Majoras-Other-Mask/Arduino-Piano-Example-Sketches/Original CG Files/CG_PCB/CG_PCB_Import/CG_PCB_Import.kicad_pcb

## KiCad design narcise/narcise-redux.kicad_pcb

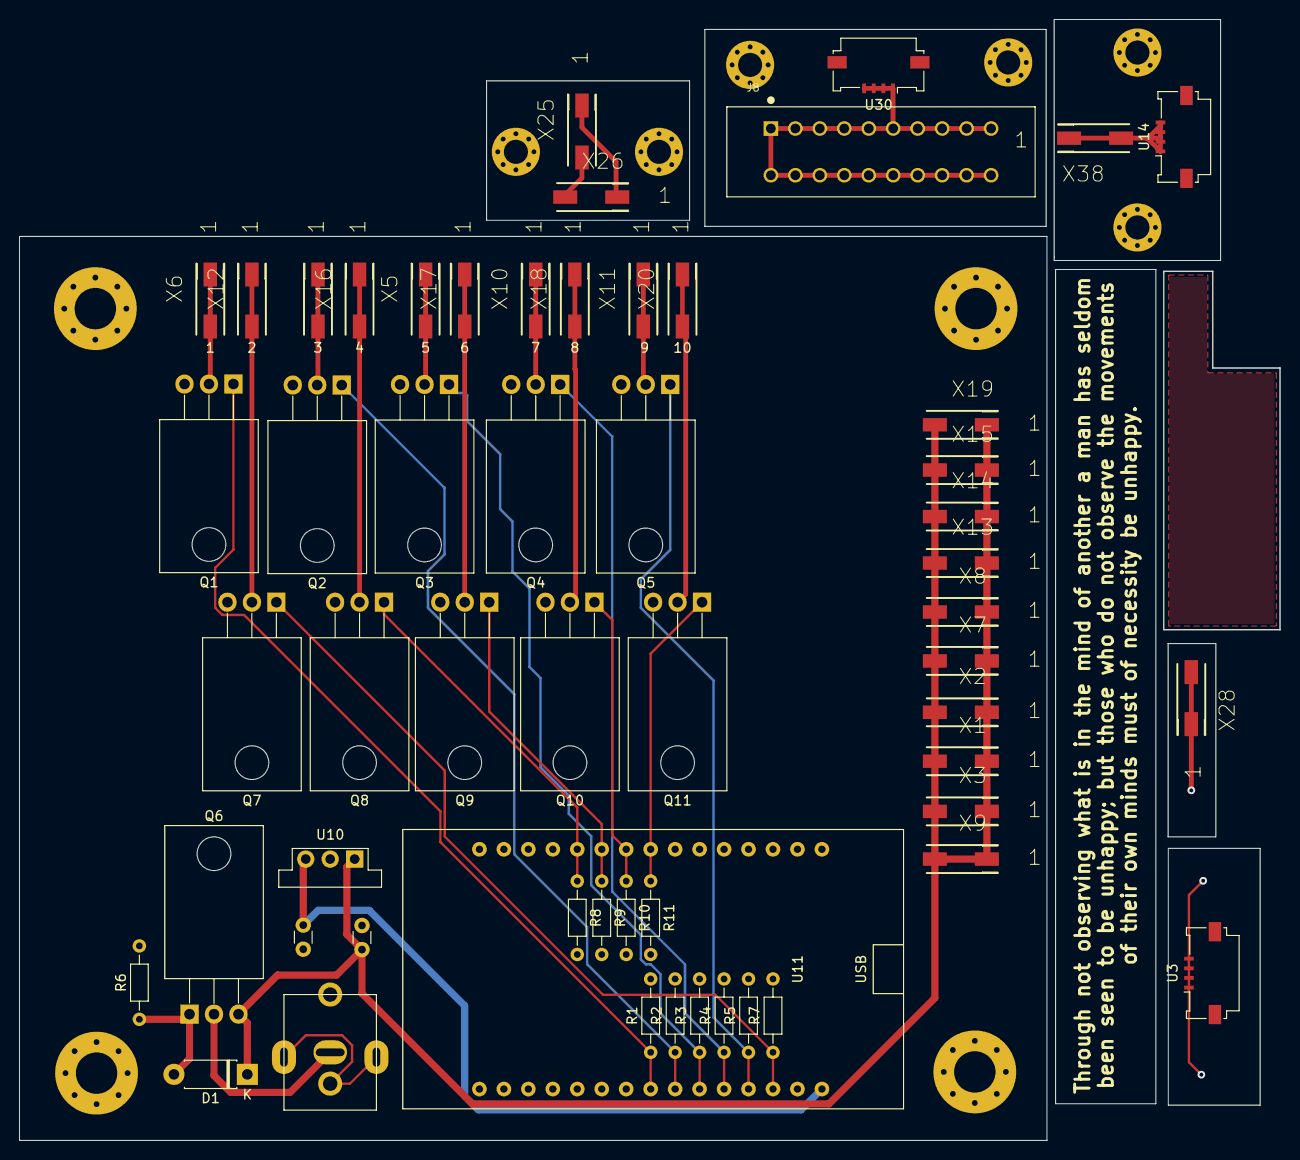
[picture p11: board narcise-redux.kicad_pcb from above]

Board: 2 copper layers, 130.9 x 116.4 mm, 56 parts (0 on the bottom side), 31 nets.

Parts:
D1: D_Zener-10V; D_DO-41_SOD81_P7.62mm_Horizontal
J8: 5-5530843-0; TE_5-5530843-0
Murata-Ceramic-Capacitor-50v1-22uF1, Murata-Ceramic-Capacitor-50v1-22uF2: C; C_Disc_D3.0mm_W1.6mm_P2.50mm
Q1, Q2, Q3, Q4, Q5, Q7, Q8, Q9, Q10, Q11: IRLZ44N-horizontal; TO-220-3_Horizontal_TabDown
Q6: IRF5305-Reverse-Polarity; TO-220-3_Horizontal_TabDown
R1, R2, R3, R4, R5, R7, R8, R9, R10, R11: R; R_Axial_DIN0204_L3.6mm_D1.6mm_P7.62mm_Horizontal
R6: 100K; R_Axial_DIN0204_L3.6mm_D1.6mm_P7.62mm_Horizontal
U3, U14: fpc-connector-mosfet-drain; Molex_200528-0040_1x04-1MP_P1.00mm_Horizontal
U10: OKI-78SR-5v; Converter_DCDC_muRata_OKI-78SR_Vertical
U11: ariadne-rescue_ESP32-WROOM-32D-ariadne; ESP32-DEVKIT
U21: POWER_CONNECTOR-DCJ250-20-B-K1-A; POWER_JACK_DCJ250-20-B-K1-A
U30: fpc-connector-VIN; Molex_200528-0040_1x04-1MP_P1.00mm_Horizontal
X1, X2, X3, X4, X5, X6, X7, X8, X9, X10, X11, X12, X13, X14, X15, X16, X17, X18, X19, X20, X25, X26, X28, X38: 2059-301_998-403; 998-403

Connections:
+5V: Murata-Ceramic-Capacitor-50v1-22uF2.1, U10.3, U11.15
+24V: D1.1, Murata-Ceramic-Capacitor-50v1-22uF1.1, Q6.3, U10.1, X1.L1.1, X1.L1.2, X2.L1.1, X2.L1.2, X3.L1.1, X3.L1.2, X7.L1.1, X7.L1.2, X8.L1.1, X8.L1.2, X9.L1.1, X9.L1.2, X13.L1.1, X13.L1.2, X14.L1.1, X14.L1.2, X15.L1.1, X15.L1.2, X19.L1.1, X19.L1.2
unnamed: D1.2, Q6.1, R6.1
unnamed: J8.1, J8.2, J8.3, J8.4, J8.5, J8.6, J8.7, J8.8, J8.9, J8.10, J8.11, J8.12, J8.13, J8.14, J8.15, J8.16, J8.17, J8.18, J8.19, J8.20, U30.1, U30.2, U30.3, U30.4
unnamed: Q1.2, X6.L1.1, X6.L1.2
unnamed: Q2.2, X4.L1.1, X4.L1.2
unnamed: Q3.2, X5.L1.1, X5.L1.2
unnamed: Q4.2, X10.L1.1, X10.L1.2
unnamed: Q5.2, X11.L1.1, X11.L1.2
unnamed: Q7.2, X12.L1.1, X12.L1.2
unnamed: Q8.2, X16.L1.1, X16.L1.2
unnamed: Q9.2, X17.L1.1, X17.L1.2
unnamed: Q10.2, X18.L1.1, X18.L1.2
unnamed: Q11.2, X20.L1.1, X20.L1.2
unnamed: U3.1, U3.2, U3.3, U3.4
unnamed: U14.1, U14.2, U14.3, U14.4, X38.L1.1, X38.L1.2
unnamed: X25.L1.1, X26.L1.1
unnamed: X25.L1.2, X26.L1.2
unnamed: X28.L1.1, X28.L1.2
POWER-IN+: Q6.2, U21.1
POWER-IN-: Murata-Ceramic-Capacitor-50v1-22uF1.2, Murata-Ceramic-Capacitor-50v1-22uF2.2, Q1.3, Q2.3, Q3.3, Q4.3, Q5.3, Q7.3, Q8.3, Q9.3, Q10.3, Q11.3, R1.2, R2.2, R3.2, R4.2, R5.2, R6.2, R7.2, R8.2, R9.2, R10.2, R11.2, U10.2, U11.14, U11.17, U21.2
sheet1: Q1.1, R1.1, U11.8
sheet2: Q2.1, R2.1, U11.9
sheet3: Q3.1, R3.1, U11.10
sheet4: Q4.1, R4.1, U11.11
sheet5: Q5.1, R5.1, U11.12
sheet6: Q7.1, R7.1, U11.13
sheet7: Q8.1, R8.1, U11.26
sheet8: Q9.1, R9.1, U11.25
sheet9: Q10.1, R10.1, U11.24
sheet10: Q11.1, R11.1, U11.23
