Majoras-Other-Mask/Arduino-Piano-Example-Sketches/Teensy Intermediate Steps/Teensy_Synth/DSP.ino

/*********************************************
 * Plays Sine Tone on Arduino Pocket Piano
 * Author: Owen Osborn, Copyright: GPL 
 * 
 *  This uses Direct Digital Synthesis (DDS)  for tone generation
 * 
 *   
 * 5 October 2007
 *
 * FOR MCP4921 DAC
 *
 * Chip type           : ATMEGA168
 * Clock frequency     : 16MHz
 *********************************************/

#define SPI_SCK 5
#define SPI_MOSI 3
int m; //counter

// Here are variables for digital audio.  
// They are declared using normal AVR-GCC notation ('uint8_t' for unsigned 8 bit number)

// Here is the sine wave and triangle wave.  It is a one cycle of sine tone, 255 8 bit samples, in hex values
// you could put any wave form you line in here...
uint8_t sawTable[]={
  0xff,0xfe,0xfd,0xfc,0xfb,0xfa,0xf9,0xf8,0xf7,0xf6,0xf5,0xf4,0xf3,0xf2,0xf1,0xf0,
  0xef,0xee,0xed,0xec,0xeb,0xea,0xe9,0xe8,0xe7,0xe6,0xe5,0xe4,0xe3,0xe2,0xe1,0xe0,
  0xdf,0xde,0xdd,0xdc,0xdb,0xda,0xd9,0xd8,0xd7,0xd6,0xd5,0xd4,0xd3,0xd2,0xd1,0xd0,
  0xcf,0xce,0xcd,0xcc,0xcb,0xca,0xc9,0xc8,0xc7,0xc6,0xc5,0xc4,0xc3,0xc2,0xc1,0xc0,
  0xbf,0xbe,0xbd,0xbc,0xbb,0xba,0xb9,0xb8,0xb7,0xb6,0xb5,0xb4,0xb3,0xb2,0xb1,0xb0,
  0xaf,0xae,0xad,0xac,0xab,0xaa,0xa9,0xa8,0xa7,0xa6,0xa5,0xa4,0xa3,0xa2,0xa1,0xa0,
  0x9f,0x9e,0x9d,0x9c,0x9b,0x9a,0x99,0x98,0x97,0x96,0x95,0x94,0x93,0x92,0x91,0x90,
  0x8f,0x8e,0x8d,0x8c,0x8b,0x8a,0x89,0x88,0x87,0x86,0x85,0x84,0x83,0x82,0x81,0x80,
  0x7f,0x7e,0x7d,0x7c,0x7b,0x7a,0x79,0x78,0x77,0x76,0x75,0x74,0x73,0x72,0x71,0x70,
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
uint8_t dacSPI0;
uint8_t dacSPI1;

// variables for oscillators
uint16_t accumulator[] = {0, 0, 0, 0};  // large number holds phase
uint8_t ind[] = {0, 0, 0, 0};   // index for wave lookup (the upper 8 bits of the accumulator)
uint16_t oscil[] = {0, 0, 0, 0};   // oscillator output
   

// timer 2 is audio interrupt timer
void sendNote() {
  if (mode == 0 || mode == 1) { 
    // calculate frequency mod
    for (m=0; m<4; m++) { 
      accumulator[m] = accumulator[m] + freq[m];
      Serial.println(accumulator[0]); 
      ind[m] = accumulator[m] >> 8;
      oscil[m] = waveFormFunc(ind[m], waveForm); 
    }
//    sample = (oscil[0] + oscil[1] + oscil[2] + oscil[3]) << 6;
     
    sample = (oscil[0] + oscil[1] + oscil[2] + oscil[3]); //uncomment when using internal DAC

  
  } else if (mode == 2) { 

    phaseDeltaModulator = (freq[0] * knob1) >> 6;   // calculate modulator frequency for a  given harmonicity
    phaseDeltaCarrier = freq[0];                           // this is just pitch (although not in Hz)
    // calculate frequency mod
    phaseAccumModulator = phaseAccumModulator + phaseDeltaModulator; 
    indexModulator = phaseAccumModulator >> 8;
    modulator = waveFormFunc(indexModulator, waveForm);
    modulator = (modulator * knob2) >> 3;
    modulatorSigned = modulator - ((128 * knob2) >> 3);   // center at 0
  
    // get carrier frequency
    phaseDeltaCarrier += modulatorSigned;
  
    // calculate carrier
    phaseAccumCarrier = phaseAccumCarrier+ (phaseDeltaCarrier);
    indexCarrier = phaseAccumCarrier >> 8;
    carrier = waveFormFunc(indexCarrier, waveForm);
    // output gain
    sample = (carrier) * gn; //
   
  }

  analogWrite(A22, sample); //uncomment when using internal DAC
  
//  // format sample for SPI port
//  dacSPI0 = sample >> 8;
//  dacSPI0 >>= 4;
//  dacSPI0 |= 0x30;
//  dacSPI1 = sample >> 4;
//
//  SPI.beginTransaction(SPISettings(4000000, MSBFIRST, SPI_MODE0));
//  digitalWriteFast(slaveSelectPin, LOW);
//  SPI.transfer(dacSPI0);
//  SPI.transfer(dacSPI1);
//  digitalWriteFast(slaveSelectPin, HIGH);
//  SPI.endTransaction();
}
